ThomasStolt/LongTermEnvLogger/images/LTL Revision 1.1.jpg

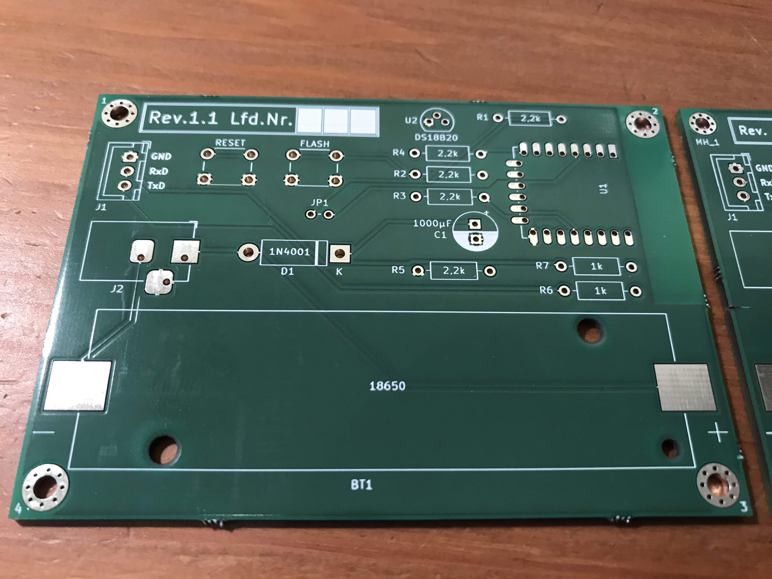
images/LTL Revision 1.1.jpg
