ThomasStolt/LongTermEnvLogger/images/LTL Revision 1.1_corr.jpg

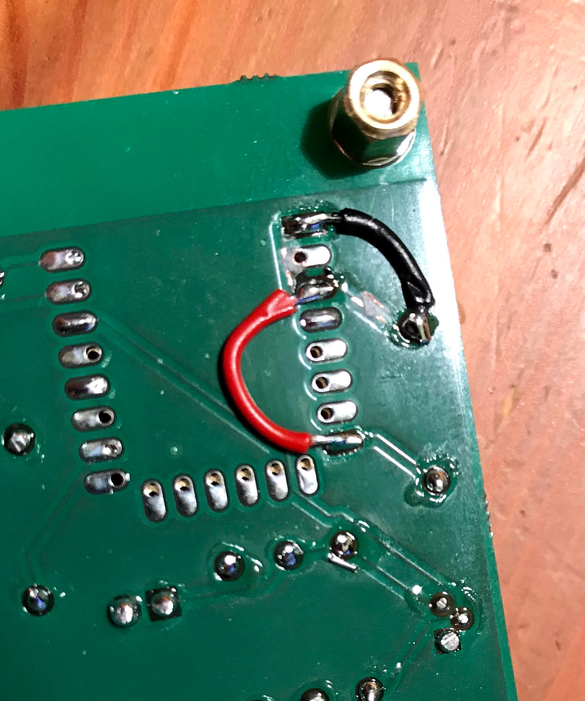
images/LTL Revision 1.1_corr.jpg
