ThomasStolt/LongTermEnvLogger/images/LTL Revision 1.2.jpg

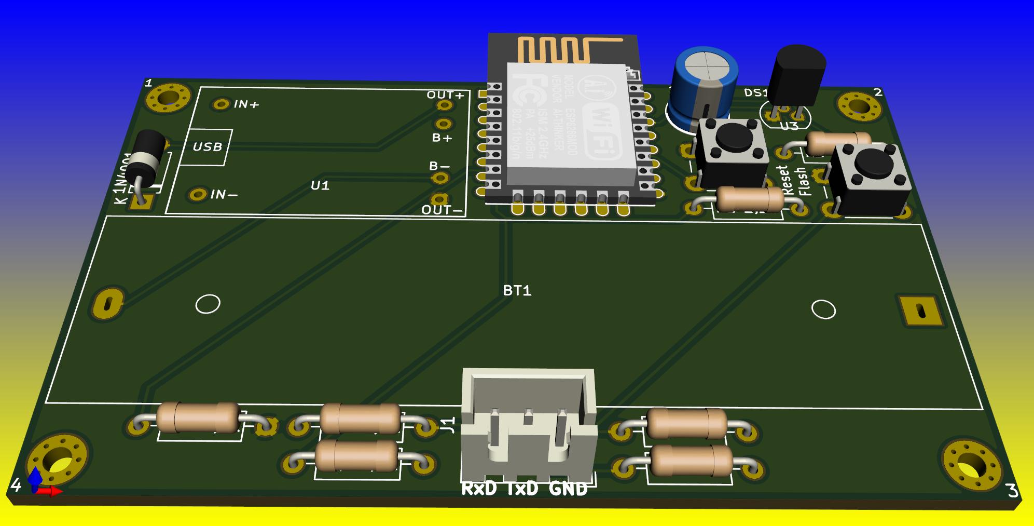
images/LTL Revision 1.2.jpg
