ThomasStolt/LongTermEnvLogger/images/LTL Revision 2.2.png

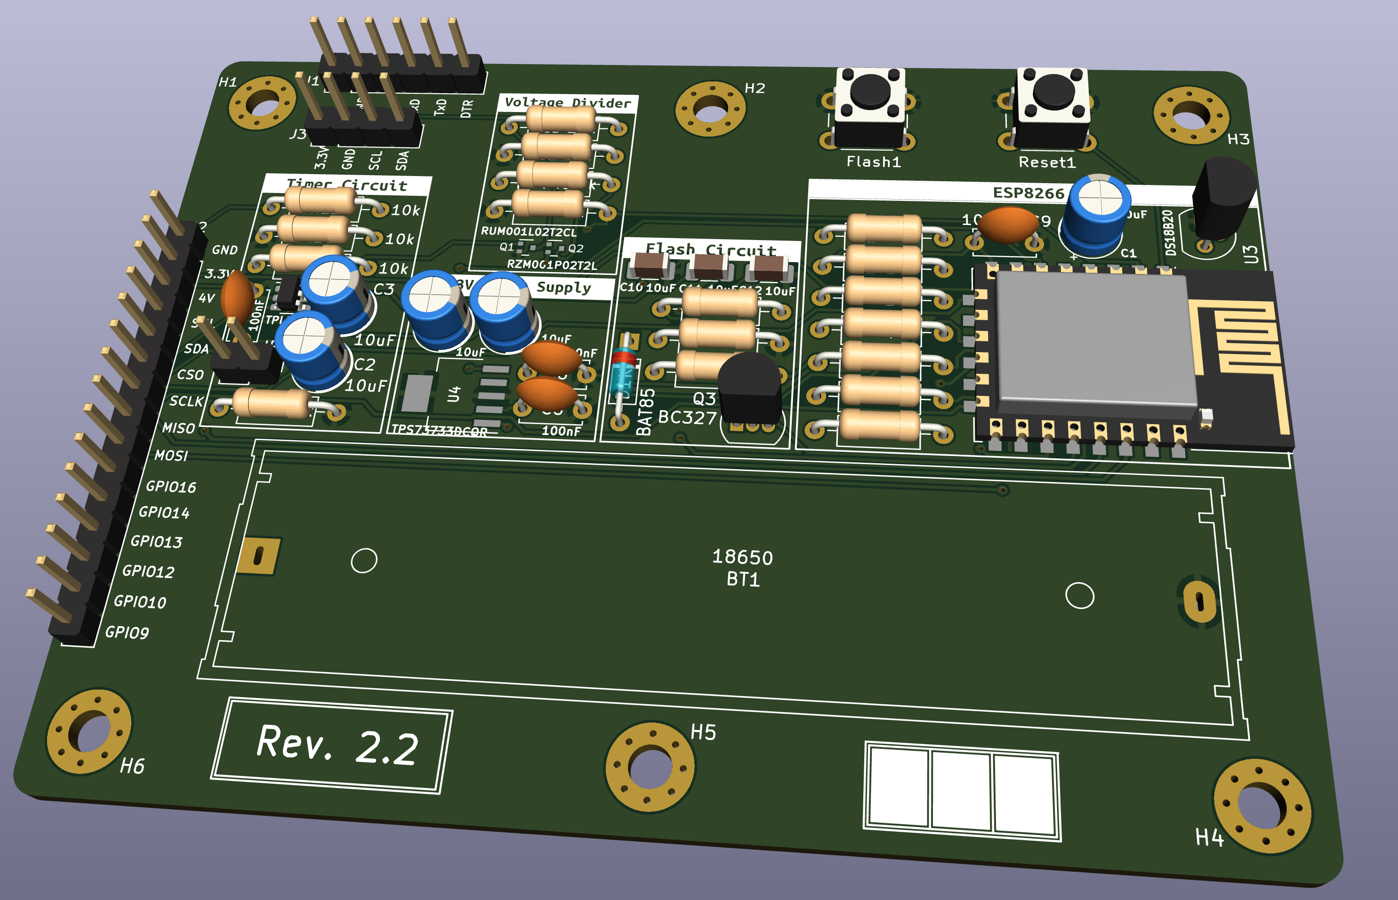
images/LTL Revision 2.2.png
