ThomasStolt/LongTermEnvLogger/images/SKYRC_MC3000.jpeg

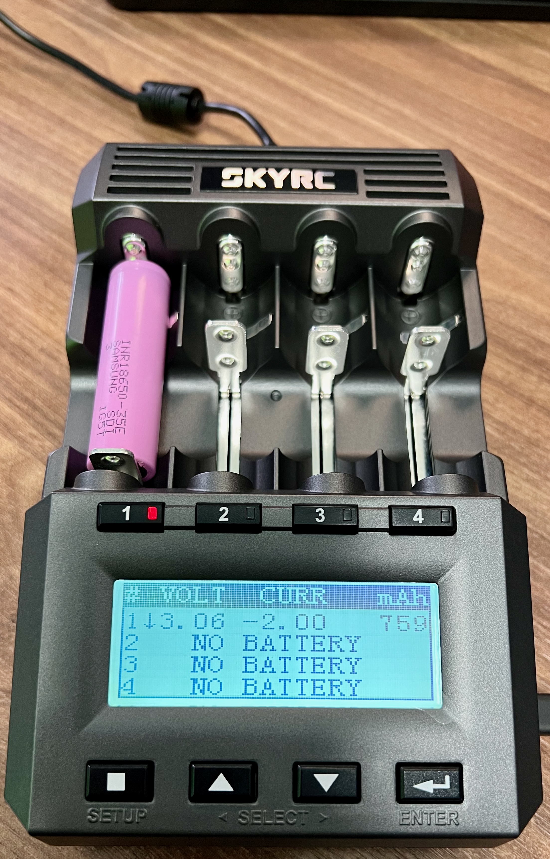
images/SKYRC_MC3000.jpeg
