ThomasStolt/LongTermEnvLogger/images/USB UART Adapter.jpeg

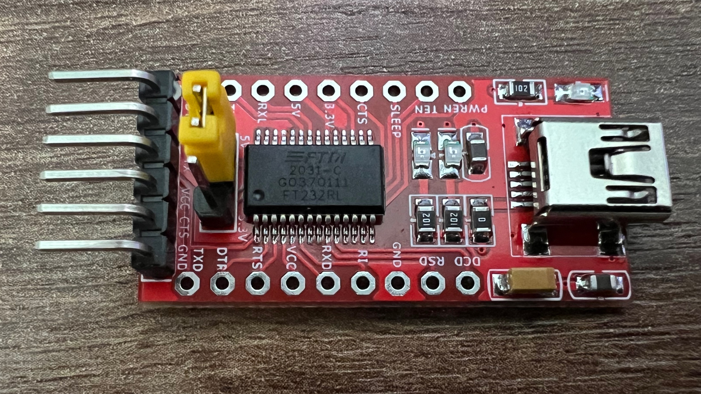
images/USB UART Adapter.jpeg
