ThomasStolt/LongTermEnvLogger/images/LTL Revision 2.1 - Build.jpeg

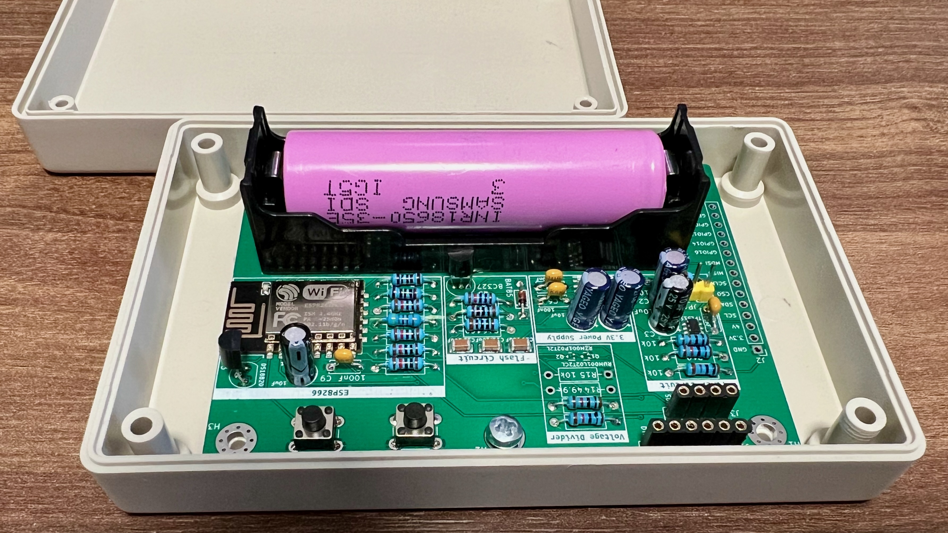
images/LTL Revision 2.1 - Build.jpeg
